jbawgs/esp32-smoker-controls/src/InputManager.h

#pragma once
#include <AiEsp32RotaryEncoder.h>
#include <AiEsp32RotaryEncoderNumberSelector.h>
#include <Constants.h>

#define ROTARY_ENCODER_A_PIN 25
#define ROTARY_ENCODER_B_PIN 26
#define ROTARY_ENCODER_BUTTON_PIN 13
#define ROTARY_ENCODER_STEPS 4
#define ROTARY_ENCODER_VCC_PIN -1
#define INIT_TEMP 250

class InputManager
{
public:
    AiEsp32RotaryEncoder *rotaryEncoder = new AiEsp32RotaryEncoder(ROTARY_ENCODER_A_PIN, ROTARY_ENCODER_B_PIN, ROTARY_ENCODER_BUTTON_PIN, ROTARY_ENCODER_VCC_PIN, ROTARY_ENCODER_STEPS);
    InputManager();
    AiEsp32RotaryEncoderNumberSelector numberSelector = AiEsp32RotaryEncoderNumberSelector();
    
    void begin();
    float getFrequency();
    void rotary_onButtonClick();
    float getInput(int tempSet);
};
void IRAM_ATTR readEncoderISR();
extern InputManager Input;
