jbawgs/esp32-smoker-controls/src/FileManager.cpp

#include <FileManager.h>

void FileManager::begin(){
if (!SD.begin(4))
  {
    Serial.println("Card Mount Failed");
    return;
  }
  uint8_t cardType = SD.cardType();

  Serial.println(cardType);

  if (cardType == CARD_NONE)
  {
    Serial.println("No SD card attached");
    return;
  }

  Serial.print("SD Card Type: ");
  if (cardType == CARD_MMC)
  {
    Serial.println("MMC");
  }
  else if (cardType == CARD_SD)
  {
    Serial.println("SDSC");
  }
  else if (cardType == CARD_SDHC)
  {
    Serial.println("SDHC");
  }
  else
  {
    Serial.println("UNKNOWN");
  }

  uint64_t cardSize = SD.cardSize() / (1024 * 1024);
  Serial.printf("SD Card Size: %lluMB\n", cardSize);
  Serial.println("1");
}

FileManager Files;
